garbage2garbage/shruti1/hardware/shruti/shruti1/resources.h

// Copyright 2009 Olivier Gillet.
//
// Author: Olivier Gillet (ol.gillet@gmail.com)
//
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
// -----------------------------------------------------------------------------
//
// Resources definitions.
//
// Automatically generated with:
// python arc.py resources.py


#ifndef HARDWARE_SHRUTI_SHRUTI1_RESOURCES_H_
#define HARDWARE_SHRUTI_SHRUTI1_RESOURCES_H_


#include "hardware/base/base.h"

#include <avr/pgmspace.h>


#include "hardware/resources/resources_manager.h"
namespace hardware_shruti {

typedef uint8_t ResourceId;

extern const prog_char* string_table[];

extern const prog_uint16_t* lookup_table_table[];

extern const prog_uint8_t* waveform_table[];

extern const prog_uint8_t* character_table[];

extern const prog_uint16_t lut_res_lfo_increments[] PROGMEM;
extern const prog_uint16_t lut_res_env_portamento_increments[] PROGMEM;
extern const prog_uint16_t lut_res_oscillator_increments[] PROGMEM;
extern const prog_uint16_t lut_res_fm_frequency_ratios[] PROGMEM;
extern const prog_uint16_t lut_res_scale_just[] PROGMEM;
extern const prog_uint16_t lut_res_scale_pythagorean[] PROGMEM;
extern const prog_uint16_t lut_res_scale_1_4_eb[] PROGMEM;
extern const prog_uint16_t lut_res_scale_1_4_e[] PROGMEM;
extern const prog_uint16_t lut_res_scale_1_4_ea[] PROGMEM;
extern const prog_uint16_t lut_res_scale_kanakangi[] PROGMEM;
extern const prog_uint16_t lut_res_scale_vanaspati[] PROGMEM;
extern const prog_uint16_t lut_res_scale_tanarupi[] PROGMEM;
extern const prog_uint16_t lut_res_scale_jhankaradhwani[] PROGMEM;
extern const prog_uint16_t lut_res_scale_kharaharapriya[] PROGMEM;
extern const prog_uint16_t lut_res_scale_varunapriya[] PROGMEM;
extern const prog_uint16_t lut_res_scale_yagapriya[] PROGMEM;
extern const prog_uint16_t lut_res_scale_vagadheeswari[] PROGMEM;
extern const prog_uint16_t lut_res_scale_chalanata[] PROGMEM;
extern const prog_uint16_t lut_res_arpeggiator_patterns[] PROGMEM;
extern const prog_uint8_t wav_res_formant_sine[] PROGMEM;
extern const prog_uint8_t wav_res_formant_square[] PROGMEM;
extern const prog_uint8_t wav_res_bandlimited_pulse_1[] PROGMEM;
extern const prog_uint8_t wav_res_bandlimited_pulse_2[] PROGMEM;
extern const prog_uint8_t wav_res_bandlimited_pulse_3[] PROGMEM;
extern const prog_uint8_t wav_res_bandlimited_pulse_4[] PROGMEM;
extern const prog_uint8_t wav_res_bandlimited_pulse_5[] PROGMEM;
extern const prog_uint8_t wav_res_bandlimited_pulse_6[] PROGMEM;
extern const prog_uint8_t wav_res_bandlimited_square_0[] PROGMEM;
extern const prog_uint8_t wav_res_bandlimited_square_1[] PROGMEM;
extern const prog_uint8_t wav_res_bandlimited_square_2[] PROGMEM;
extern const prog_uint8_t wav_res_bandlimited_square_3[] PROGMEM;
extern const prog_uint8_t wav_res_bandlimited_square_4[] PROGMEM;
extern const prog_uint8_t wav_res_bandlimited_square_5[] PROGMEM;
extern const prog_uint8_t wav_res_bandlimited_square_6[] PROGMEM;
extern const prog_uint8_t wav_res_bandlimited_saw_0[] PROGMEM;
extern const prog_uint8_t wav_res_bandlimited_saw_1[] PROGMEM;
extern const prog_uint8_t wav_res_bandlimited_saw_2[] PROGMEM;
extern const prog_uint8_t wav_res_bandlimited_saw_3[] PROGMEM;
extern const prog_uint8_t wav_res_bandlimited_saw_4[] PROGMEM;
extern const prog_uint8_t wav_res_bandlimited_saw_5[] PROGMEM;
extern const prog_uint8_t wav_res_bandlimited_triangle_0[] PROGMEM;
extern const prog_uint8_t wav_res_bandlimited_triangle_1[] PROGMEM;
extern const prog_uint8_t wav_res_bandlimited_triangle_2[] PROGMEM;
extern const prog_uint8_t wav_res_bandlimited_triangle_3[] PROGMEM;
extern const prog_uint8_t wav_res_bandlimited_triangle_4[] PROGMEM;
extern const prog_uint8_t wav_res_bandlimited_triangle_5[] PROGMEM;
extern const prog_uint8_t wav_res_wavetable[] PROGMEM;
extern const prog_uint8_t wav_res_vowel_data[] PROGMEM;
extern const prog_uint8_t chr_res_special_characters[] PROGMEM;
#define STR_RES_ATK 0  // atk
#define STR_RES_WV1 1  // wv1
#define STR_RES_RT1 2  // rt1
#define STR_RES_WV2 3  // wv2
#define STR_RES_RT2 4  // rt2
#define STR_RES_SRC 5  // src
#define STR_RES_DST 6  // dst
#define STR_RES_AMT 7  // amt
#define STR_RES_CHN 8  // chn
#define STR_RES_BPM 9  // bpm
#define STR_RES_SWG 10  // swg
#define STR_RES_SHAPE 11  // shape
#define STR_RES_ENV1TVCF 12  // env1~vcf
#define STR_RES_LFO2TVCF 13  // lfo2~vcf
#define STR_RES_RESONANCE 14  // resonance
#define STR_RES_ENVELOPE_1 15  // envelope 1
#define STR_RES_ENVELOPE_2 16  // envelope 2
#define STR_RES_SEQUENCER 17  // sequencer
#define STR_RES_ATTACK 18  // attack
#define STR_RES_DECAY 19  // decay
#define STR_RES_SUSTAIN 20  // sustain
#define STR_RES_RELEASE 21  // release
#define STR_RES_LFO1_WAVE 22  // lfo1 wave
#define STR_RES_LFO1_RATE 23  // lfo1 rate
#define STR_RES_LFO2_WAVE 24  // lfo2 wave
#define STR_RES_LFO2_RATE 25  // lfo2 rate
#define STR_RES_MOD_ 26  // mod.
#define STR_RES_SOURCE 27  // source
#define STR_RES_DEST_ 28  // dest.
#define STR_RES_AMOUNT 29  // amount
#define STR_RES_OCTAVE 30  // octave
#define STR_RES_RAGA 31  // raga
#define STR_RES_MIDI_CHAN 32  // midi chan
#define STR_RES_TEMPO 33  // tempo
#define STR_RES_MIXER 34  // mixer
#define STR_RES_FILTER 35  // filter
#define STR_RES_LFOS 36  // lfos
#define STR_RES_MODULATION 37  // modulation
#define STR_RES_KEYBOARD 38  // keyboard
#define STR_RES_OFF 39  // off
#define STR_RES_ON 40  // on
#define STR_RES_TRI 41  // tri
#define STR_RES_SQR 42  // sqr
#define STR_RES_S_H 43  // s&h
#define STR_RES_3 44  // 
#define STR_RES_LF1 45  // lf1
#define STR_RES_LF2 46  // lf2
#define STR_RES_SEQ 47  // seq
#define STR_RES_ARP 48  // arp
#define STR_RES_WHL 49  // whl
#define STR_RES_BND 50  // bnd
#define STR_RES_AS1 51  // as1
#define STR_RES_AS2 52  // as2
#define STR_RES_CV1 53  // cv1
#define STR_RES_CV2 54  // cv2
#define STR_RES_RND 55  // rnd
#define STR_RES_EN1 56  // en1
#define STR_RES_EN2 57  // en2
#define STR_RES_VEL 58  // vel
#define STR_RES_NOT 59  // not
#define STR_RES_GAT 60  // gat
#define STR_RES_LFO1 61  // lfo1
#define STR_RES_LFO2 62  // lfo2
#define STR_RES_STPSEQ 63  // stpseq
#define STR_RES__ARP 64  //  arp
#define STR_RES_MWHEEL 65  // mwheel
#define STR_RES_BENDER 66  // bender
#define STR_RES_ASSGN1 67  // assgn1
#define STR_RES_ASSGN2 68  // assgn2
#define STR_RES__CV1 69  //  cv1
#define STR_RES__CV2 70  //  cv2
#define STR_RES_RANDOM 71  // random
#define STR_RES_ENV1 72  // env1
#define STR_RES_ENV2 73  // env2
#define STR_RES_VELO 74  // velo
#define STR_RES_NOTE 75  // note
#define STR_RES_GATE 76  // gate
#define STR_RES_P_ORLEANS_21_MN 77  // P.ORLEANS: 21 MN
#define STR_RES_P_BERCY_____S1H 78  // P.BERCY:     +1H
#define STR_RES_LOAD_SAVE_PATCH 79  // load/save patch
#define STR_RES_STEP_SEQUENCER 80  // step sequencer
#define STR_RES_LOAD 81  // load
#define STR_RES_EXIT 82  // exit
#define STR_RES_SAVE 83  // save
#define STR_RES_EXTERN 84  // extern
#define STR_RES_EQUAL 85  // equal
#define STR_RES_JUST 86  // just
#define STR_RES_PYTHAG 87  // pythag
#define STR_RES_1_4_EB 88  // 1/4 eb
#define STR_RES_1_4_E 89  // 1/4 e
#define STR_RES_1_4_EA 90  // 1/4 ea
#define STR_RES_KANAKA 91  // kanaka
#define STR_RES_RATNAN 92  // ratnan
#define STR_RES_GANAMU 93  // ganamu
#define STR_RES_VANASP 94  // vanasp
#define STR_RES_MANAVA 95  // manava
#define STR_RES_TANARU 96  // tanaru
#define STR_RES_SENAVA 97  // senava
#define STR_RES_HANUMA 98  // hanuma
#define STR_RES_DHENUK 99  // dhenuk
#define STR_RES_NATAKA 100  // nataka
#define STR_RES_KOKILA 101  // kokila
#define STR_RES_RUPAVA 102  // rupava
#define STR_RES_GAYAKA 103  // gayaka
#define STR_RES_VAKULA 104  // vakula
#define STR_RES_MAYAMA 105  // mayama
#define STR_RES_CHAKRA 106  // chakra
#define STR_RES_SURYAK 107  // suryak
#define STR_RES_HATAKA 108  // hataka
#define STR_RES_JHANKA 109  // jhanka
#define STR_RES_NATABH 110  // natabh
#define STR_RES_KEERAV 111  // keerav
#define STR_RES_KHARAH 112  // kharah
#define STR_RES_GOURIM 113  // gourim
#define STR_RES_VARUNA 114  // varuna
#define STR_RES_MARARA 115  // marara
#define STR_RES_CHARUK 116  // charuk
#define STR_RES_SARASA 117  // sarasa
#define STR_RES_HARIKA 118  // harika
#define STR_RES_DHEERA 119  // dheera
#define STR_RES_NAGANA 120  // nagana
#define STR_RES_YAGAPR 121  // yagapr
#define STR_RES_RAGAVA 122  // ragava
#define STR_RES_GANGEY 123  // gangey
#define STR_RES_VAGADH 124  // vagadh
#define STR_RES_SHULIN 125  // shulin
#define STR_RES_CHALAN 126  // chalan
#define STR_RES_SALAGA 127  // salaga
#define STR_RES_JALARN 128  // jalarn
#define STR_RES_JHALAV 129  // jhalav
#define STR_RES_NAVANE 130  // navane
#define STR_RES_PAVANI 131  // pavani
#define STR_RES_RAGHUP 132  // raghup
#define STR_RES_GAVAMB 133  // gavamb
#define STR_RES_BHAVAP 134  // bhavap
#define STR_RES_SHUBHA 135  // shubha
#define STR_RES_SHADVI 136  // shadvi
#define STR_RES_SUVARN 137  // suvarn
#define STR_RES_DIVYAM 138  // divyam
#define STR_RES_DHAVAL 139  // dhaval
#define STR_RES_NAMANA 140  // namana
#define STR_RES_KAMAVA 141  // kamava
#define STR_RES_RAMAPR 142  // ramapr
#define STR_RES_GAMANA 143  // gamana
#define STR_RES_VISHWA 144  // vishwa
#define STR_RES_SHAMAL 145  // shamal
#define STR_RES_SHANMU 146  // shanmu
#define STR_RES_SIMHEN 147  // simhen
#define STR_RES_HEMAVA 148  // hemava
#define STR_RES_DHARMA 149  // dharma
#define STR_RES_NEETIM 150  // neetim
#define STR_RES_KANTAM 151  // kantam
#define STR_RES_RISHAB 152  // rishab
#define STR_RES_LATANG 153  // latang
#define STR_RES_VACHAS 154  // vachas
#define STR_RES_MECHAK 155  // mechak
#define STR_RES_CHITRA 156  // chitra
#define STR_RES_SUCHAR 157  // suchar
#define STR_RES_JYOTIS 158  // jyotis
#define STR_RES_DHATUV 159  // dhatuv
#define STR_RES_NASIKA 160  // nasika
#define STR_RES_KOSALA 161  // kosala
#define STR_RES_RASIKA 162  // rasika
#define STR_RES_PRM 163  // prm
#define STR_RES_RNG 164  // rng
#define STR_RES_OP 165  // op
#define STR_RES_TUN 166  // tun
#define STR_RES_PRT 167  // prt
#define STR_RES_PORTA 168  // porta
#define STR_RES_PARAMETER 169  // parameter
#define STR_RES_RANGE 170  // range
#define STR_RES_OPERATOR 171  // operator
#define STR_RES_DETUNE 172  // detune
#define STR_RES_OSC_BAL 173  // osc bal
#define STR_RES_SUB_OSC_ 174  // sub osc.
#define STR_RES_PATTERN 175  // pattern
#define STR_RES_SWING 176  // swing
#define STR_RES_OSCILLATOR_1 177  // oscillator 1
#define STR_RES_OSCILLATOR_2 178  // oscillator 2
#define STR_RES_ARPEGGIO 179  // arpeggio
#define STR_RES_NONE 180  // none
#define STR_RES_BLIT 181  // blit
#define STR_RES_SAW 182  // saw
#define STR_RES_SQUARE 183  // square
#define STR_RES_TRIANG 184  // triang
#define STR_RES_CZ 185  // cz
#define STR_RES_FM 186  // fm
#define STR_RES_8BITS 187  // 8bits
#define STR_RES_PWM 188  // pwm
#define STR_RES_NOISE 189  // noise
#define STR_RES_VOWEL 190  // vowel
#define STR_RES_TABLE 191  // table
#define STR_RES_SWEEP 192  // sweep
#define STR_RES_1S2 193  // 1+2
#define STR_RES_1_2 194  // 1>2
#define STR_RES_1P2 195  // 1*2
#define STR_RES_1X2 196  // 1^2
#define STR_RES_CUT 197  // cut
#define STR_RES_VCA 198  // vca
#define STR_RES_PW1 199  // pw1
#define STR_RES_PW2 200  // pw2
#define STR_RES_51 201  // 1
#define STR_RES_52 202  // 2
#define STR_RES_5 203  // 
#define STR_RES_MIX 204  // mix
#define STR_RES_NOI 205  // noi
#define STR_RES_SUB 206  // sub
#define STR_RES_RES 207  // res
#define STR_RES_CUTOFF 208  // cutoff
#define STR_RES__VCA 209  //  vca
#define STR_RES_PWM1 210  // pwm1
#define STR_RES_PWM2 211  // pwm2
#define STR_RES_OSC1 212  // osc1
#define STR_RES_OSC2 213  // osc2
#define STR_RES_OSC1S2 214  // osc1+2
#define STR_RES__MIX 215  //  mix
#define STR_RES__NOISE 216  //  noise
#define STR_RES_SUBOSC 217  // subosc
#define STR_RES_RESO 218  // reso
#define STR_RES_MUTABLE 219  // mutable
#define STR_RES_INSTRUMENTS_671 220  // instruments -1
#define LUT_RES_LFO_INCREMENTS 0
#define LUT_RES_LFO_INCREMENTS_SIZE 128
#define LUT_RES_ENV_PORTAMENTO_INCREMENTS 1
#define LUT_RES_ENV_PORTAMENTO_INCREMENTS_SIZE 128
#define LUT_RES_OSCILLATOR_INCREMENTS 2
#define LUT_RES_OSCILLATOR_INCREMENTS_SIZE 768
#define LUT_RES_FM_FREQUENCY_RATIOS 3
#define LUT_RES_FM_FREQUENCY_RATIOS_SIZE 25
#define LUT_RES_SCALE_JUST 4
#define LUT_RES_SCALE_JUST_SIZE 12
#define LUT_RES_SCALE_PYTHAGOREAN 5
#define LUT_RES_SCALE_PYTHAGOREAN_SIZE 12
#define LUT_RES_SCALE_1_4_EB 6
#define LUT_RES_SCALE_1_4_EB_SIZE 12
#define LUT_RES_SCALE_1_4_E 7
#define LUT_RES_SCALE_1_4_E_SIZE 12
#define LUT_RES_SCALE_1_4_EA 8
#define LUT_RES_SCALE_1_4_EA_SIZE 12
#define LUT_RES_SCALE_KANAKANGI 9
#define LUT_RES_SCALE_KANAKANGI_SIZE 12
#define LUT_RES_SCALE_RATNANGI 10
#define LUT_RES_SCALE_RATNANGI_SIZE 12
#define LUT_RES_SCALE_GANAMURTI 11
#define LUT_RES_SCALE_GANAMURTI_SIZE 12
#define LUT_RES_SCALE_VANASPATI 12
#define LUT_RES_SCALE_VANASPATI_SIZE 12
#define LUT_RES_SCALE_MANAVATI 13
#define LUT_RES_SCALE_MANAVATI_SIZE 12
#define LUT_RES_SCALE_TANARUPI 14
#define LUT_RES_SCALE_TANARUPI_SIZE 12
#define LUT_RES_SCALE_SENAVATI 15
#define LUT_RES_SCALE_SENAVATI_SIZE 12
#define LUT_RES_SCALE_HANUMATODI 16
#define LUT_RES_SCALE_HANUMATODI_SIZE 12
#define LUT_RES_SCALE_DHENUKA 17
#define LUT_RES_SCALE_DHENUKA_SIZE 12
#define LUT_RES_SCALE_NATAKAPRIYA 18
#define LUT_RES_SCALE_NATAKAPRIYA_SIZE 12
#define LUT_RES_SCALE_KOKILAPRIYA 19
#define LUT_RES_SCALE_KOKILAPRIYA_SIZE 12
#define LUT_RES_SCALE_RUPAVATI 20
#define LUT_RES_SCALE_RUPAVATI_SIZE 12
#define LUT_RES_SCALE_GAYAKAPRIYA 21
#define LUT_RES_SCALE_GAYAKAPRIYA_SIZE 12
#define LUT_RES_SCALE_VAKULABHARANAM 22
#define LUT_RES_SCALE_VAKULABHARANAM_SIZE 12
#define LUT_RES_SCALE_MAYAMALAVAGOWLA 23
#define LUT_RES_SCALE_MAYAMALAVAGOWLA_SIZE 12
#define LUT_RES_SCALE_CHAKRAVAKAM 24
#define LUT_RES_SCALE_CHAKRAVAKAM_SIZE 12
#define LUT_RES_SCALE_SURYAKANTAM 25
#define LUT_RES_SCALE_SURYAKANTAM_SIZE 12
#define LUT_RES_SCALE_HATAKAMBARI 26
#define LUT_RES_SCALE_HATAKAMBARI_SIZE 12
#define LUT_RES_SCALE_JHANKARADHWANI 27
#define LUT_RES_SCALE_JHANKARADHWANI_SIZE 12
#define LUT_RES_SCALE_NATABHAIRAVI 28
#define LUT_RES_SCALE_NATABHAIRAVI_SIZE 12
#define LUT_RES_SCALE_KEERAVANI 29
#define LUT_RES_SCALE_KEERAVANI_SIZE 12
#define LUT_RES_SCALE_KHARAHARAPRIYA 30
#define LUT_RES_SCALE_KHARAHARAPRIYA_SIZE 12
#define LUT_RES_SCALE_GOURIMANOHARI 31
#define LUT_RES_SCALE_GOURIMANOHARI_SIZE 12
#define LUT_RES_SCALE_VARUNAPRIYA 32
#define LUT_RES_SCALE_VARUNAPRIYA_SIZE 12
#define LUT_RES_SCALE_MARARANJANI 33
#define LUT_RES_SCALE_MARARANJANI_SIZE 12
#define LUT_RES_SCALE_CHARUKESI 34
#define LUT_RES_SCALE_CHARUKESI_SIZE 12
#define LUT_RES_SCALE_SARASANGI 35
#define LUT_RES_SCALE_SARASANGI_SIZE 12
#define LUT_RES_SCALE_HARIKAMBHOJI 36
#define LUT_RES_SCALE_HARIKAMBHOJI_SIZE 12
#define LUT_RES_SCALE_DHEERASANKARABHARANAM 37
#define LUT_RES_SCALE_DHEERASANKARABHARANAM_SIZE 12
#define LUT_RES_SCALE_NAGANANDINI 38
#define LUT_RES_SCALE_NAGANANDINI_SIZE 12
#define LUT_RES_SCALE_YAGAPRIYA 39
#define LUT_RES_SCALE_YAGAPRIYA_SIZE 12
#define LUT_RES_SCALE_RAGAVARDHINI 40
#define LUT_RES_SCALE_RAGAVARDHINI_SIZE 12
#define LUT_RES_SCALE_GANGEYABHUSHANI 41
#define LUT_RES_SCALE_GANGEYABHUSHANI_SIZE 12
#define LUT_RES_SCALE_VAGADHEESWARI 42
#define LUT_RES_SCALE_VAGADHEESWARI_SIZE 12
#define LUT_RES_SCALE_SHULINI 43
#define LUT_RES_SCALE_SHULINI_SIZE 12
#define LUT_RES_SCALE_CHALANATA 44
#define LUT_RES_SCALE_CHALANATA_SIZE 12
#define LUT_RES_SCALE_SALAGAM 45
#define LUT_RES_SCALE_SALAGAM_SIZE 12
#define LUT_RES_SCALE_JALARNAVAM 46
#define LUT_RES_SCALE_JALARNAVAM_SIZE 12
#define LUT_RES_SCALE_JHALAVARALI 47
#define LUT_RES_SCALE_JHALAVARALI_SIZE 12
#define LUT_RES_SCALE_NAVANEETAM 48
#define LUT_RES_SCALE_NAVANEETAM_SIZE 12
#define LUT_RES_SCALE_PAVANI 49
#define LUT_RES_SCALE_PAVANI_SIZE 12
#define LUT_RES_SCALE_RAGHUPRIYA 50
#define LUT_RES_SCALE_RAGHUPRIYA_SIZE 12
#define LUT_RES_SCALE_GAVAMBHODI 51
#define LUT_RES_SCALE_GAVAMBHODI_SIZE 12
#define LUT_RES_SCALE_BHAVAPRIYA 52
#define LUT_RES_SCALE_BHAVAPRIYA_SIZE 12
#define LUT_RES_SCALE_SHUBHAPANTUVARALI 53
#define LUT_RES_SCALE_SHUBHAPANTUVARALI_SIZE 12
#define LUT_RES_SCALE_SHADVIDAMARGINI 54
#define LUT_RES_SCALE_SHADVIDAMARGINI_SIZE 12
#define LUT_RES_SCALE_SUVARNANGI 55
#define LUT_RES_SCALE_SUVARNANGI_SIZE 12
#define LUT_RES_SCALE_DIVYAMANI 56
#define LUT_RES_SCALE_DIVYAMANI_SIZE 12
#define LUT_RES_SCALE_DHAVALAMBARI 57
#define LUT_RES_SCALE_DHAVALAMBARI_SIZE 12
#define LUT_RES_SCALE_NAMANARAYANI 58
#define LUT_RES_SCALE_NAMANARAYANI_SIZE 12
#define LUT_RES_SCALE_KAMAVARDANI 59
#define LUT_RES_SCALE_KAMAVARDANI_SIZE 12
#define LUT_RES_SCALE_RAMAPRIYA 60
#define LUT_RES_SCALE_RAMAPRIYA_SIZE 12
#define LUT_RES_SCALE_GAMANASHRAMA 61
#define LUT_RES_SCALE_GAMANASHRAMA_SIZE 12
#define LUT_RES_SCALE_VISHWAMBARI 62
#define LUT_RES_SCALE_VISHWAMBARI_SIZE 12
#define LUT_RES_SCALE_SHAMALANGI 63
#define LUT_RES_SCALE_SHAMALANGI_SIZE 12
#define LUT_RES_SCALE_SHANMUKHAPRIYA 64
#define LUT_RES_SCALE_SHANMUKHAPRIYA_SIZE 12
#define LUT_RES_SCALE_SIMHENDRAMADHYAMAM 65
#define LUT_RES_SCALE_SIMHENDRAMADHYAMAM_SIZE 12
#define LUT_RES_SCALE_HEMAVATI 66
#define LUT_RES_SCALE_HEMAVATI_SIZE 12
#define LUT_RES_SCALE_DHARMAVATI 67
#define LUT_RES_SCALE_DHARMAVATI_SIZE 12
#define LUT_RES_SCALE_NEETIMATI 68
#define LUT_RES_SCALE_NEETIMATI_SIZE 12
#define LUT_RES_SCALE_KANTAMANI 69
#define LUT_RES_SCALE_KANTAMANI_SIZE 12
#define LUT_RES_SCALE_RISHABHAPRIYA 70
#define LUT_RES_SCALE_RISHABHAPRIYA_SIZE 12
#define LUT_RES_SCALE_LATANGI 71
#define LUT_RES_SCALE_LATANGI_SIZE 12
#define LUT_RES_SCALE_VACHASPATI 72
#define LUT_RES_SCALE_VACHASPATI_SIZE 12
#define LUT_RES_SCALE_MECHAKALYANI 73
#define LUT_RES_SCALE_MECHAKALYANI_SIZE 12
#define LUT_RES_SCALE_CHITRAMBARI 74
#define LUT_RES_SCALE_CHITRAMBARI_SIZE 12
#define LUT_RES_SCALE_SUCHARITRA 75
#define LUT_RES_SCALE_SUCHARITRA_SIZE 12
#define LUT_RES_SCALE_JYOTISWARUPINI 76
#define LUT_RES_SCALE_JYOTISWARUPINI_SIZE 12
#define LUT_RES_SCALE_DHATUVARDANI 77
#define LUT_RES_SCALE_DHATUVARDANI_SIZE 12
#define LUT_RES_SCALE_NASIKABHUSHANI 78
#define LUT_RES_SCALE_NASIKABHUSHANI_SIZE 12
#define LUT_RES_SCALE_KOSALAM 79
#define LUT_RES_SCALE_KOSALAM_SIZE 12
#define LUT_RES_SCALE_RASIKAPRIYA 80
#define LUT_RES_SCALE_RASIKAPRIYA_SIZE 12
#define LUT_RES_ARPEGGIATOR_PATTERNS 81
#define LUT_RES_ARPEGGIATOR_PATTERNS_SIZE 15
#define WAV_RES_FORMANT_SINE 0
#define WAV_RES_FORMANT_SINE_SIZE 256
#define WAV_RES_FORMANT_SQUARE 1
#define WAV_RES_FORMANT_SQUARE_SIZE 256
#define WAV_RES_BANDLIMITED_PULSE_1 2
#define WAV_RES_BANDLIMITED_PULSE_1_SIZE 257
#define WAV_RES_BANDLIMITED_PULSE_2 3
#define WAV_RES_BANDLIMITED_PULSE_2_SIZE 257
#define WAV_RES_BANDLIMITED_PULSE_3 4
#define WAV_RES_BANDLIMITED_PULSE_3_SIZE 257
#define WAV_RES_BANDLIMITED_PULSE_4 5
#define WAV_RES_BANDLIMITED_PULSE_4_SIZE 257
#define WAV_RES_BANDLIMITED_PULSE_5 6
#define WAV_RES_BANDLIMITED_PULSE_5_SIZE 257
#define WAV_RES_BANDLIMITED_PULSE_6 7
#define WAV_RES_BANDLIMITED_PULSE_6_SIZE 257
#define WAV_RES_BANDLIMITED_SQUARE_0 8
#define WAV_RES_BANDLIMITED_SQUARE_0_SIZE 257
#define WAV_RES_BANDLIMITED_SQUARE_1 9
#define WAV_RES_BANDLIMITED_SQUARE_1_SIZE 257
#define WAV_RES_BANDLIMITED_SQUARE_2 10
#define WAV_RES_BANDLIMITED_SQUARE_2_SIZE 257
#define WAV_RES_BANDLIMITED_SQUARE_3 11
#define WAV_RES_BANDLIMITED_SQUARE_3_SIZE 257
#define WAV_RES_BANDLIMITED_SQUARE_4 12
#define WAV_RES_BANDLIMITED_SQUARE_4_SIZE 257
#define WAV_RES_BANDLIMITED_SQUARE_5 13
#define WAV_RES_BANDLIMITED_SQUARE_5_SIZE 257
#define WAV_RES_BANDLIMITED_SQUARE_6 14
#define WAV_RES_BANDLIMITED_SQUARE_6_SIZE 257
#define WAV_RES_BANDLIMITED_SAW_0 15
#define WAV_RES_BANDLIMITED_SAW_0_SIZE 257
#define WAV_RES_BANDLIMITED_SAW_1 16
#define WAV_RES_BANDLIMITED_SAW_1_SIZE 257
#define WAV_RES_BANDLIMITED_SAW_2 17
#define WAV_RES_BANDLIMITED_SAW_2_SIZE 257
#define WAV_RES_BANDLIMITED_SAW_3 18
#define WAV_RES_BANDLIMITED_SAW_3_SIZE 257
#define WAV_RES_BANDLIMITED_SAW_4 19
#define WAV_RES_BANDLIMITED_SAW_4_SIZE 257
#define WAV_RES_BANDLIMITED_SAW_5 20
#define WAV_RES_BANDLIMITED_SAW_5_SIZE 257
#define WAV_RES_BANDLIMITED_SAW_6 21
#define WAV_RES_BANDLIMITED_SAW_6_SIZE 257
#define WAV_RES_BANDLIMITED_TRIANGLE_0 22
#define WAV_RES_BANDLIMITED_TRIANGLE_0_SIZE 257
#define WAV_RES_BANDLIMITED_TRIANGLE_1 23
#define WAV_RES_BANDLIMITED_TRIANGLE_1_SIZE 257
#define WAV_RES_BANDLIMITED_TRIANGLE_2 24
#define WAV_RES_BANDLIMITED_TRIANGLE_2_SIZE 257
#define WAV_RES_BANDLIMITED_TRIANGLE_3 25
#define WAV_RES_BANDLIMITED_TRIANGLE_3_SIZE 257
#define WAV_RES_BANDLIMITED_TRIANGLE_4 26
#define WAV_RES_BANDLIMITED_TRIANGLE_4_SIZE 257
#define WAV_RES_BANDLIMITED_TRIANGLE_5 27
#define WAV_RES_BANDLIMITED_TRIANGLE_5_SIZE 257
#define WAV_RES_BANDLIMITED_TRIANGLE_6 28
#define WAV_RES_BANDLIMITED_TRIANGLE_6_SIZE 257
#define WAV_RES_WAVETABLE 29
#define WAV_RES_WAVETABLE_SIZE 2145
#define WAV_RES_VOWEL_DATA 30
#define WAV_RES_VOWEL_DATA_SIZE 45
#define CHR_RES_SPECIAL_CHARACTERS 0
#define CHR_RES_SPECIAL_CHARACTERS_SIZE 64
typedef hardware_resources::ResourcesManager<
    ResourceId,
    hardware_resources::ResourcesTables<
        string_table,
        lookup_table_table> > ResourcesManager; 

}  // namespace hardware_shruti

#endif  // HARDWARE_SHRUTI_SHRUTI1_RESOURCES_H_
