garbage2garbage/shruti1/hardware/shruti/resources.cc

// Copyright 2009 Emilie Gillet.
//
// Author: Emilie Gillet (emilie.o.gillet@gmail.com)
//
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
// -----------------------------------------------------------------------------
//
// Resources definitions.
//
// Automatically generated with:
// make resources


#include "resources.h"

namespace hardware_shruti {

static const prog_char str_res_prm[] PROGMEM = "prm";
static const prog_char str_res_rng[] PROGMEM = "rng";
static const prog_char str_res_op[] PROGMEM = "op";
static const prog_char str_res_tun[] PROGMEM = "tun";
static const prog_char str_res_prt[] PROGMEM = "prt";
static const prog_char str_res_porta[] PROGMEM = "porta";
static const prog_char str_res_parameter[] PROGMEM = "parameter";
static const prog_char str_res_range[] PROGMEM = "range";
static const prog_char str_res_operator[] PROGMEM = "operator";
static const prog_char str_res_detune[] PROGMEM = "detune";
static const prog_char str_res_osc_bal[] PROGMEM = "osc bal";
static const prog_char str_res_sub_osc_[] PROGMEM = "sub osc.";
static const prog_char str_res_pattern[] PROGMEM = "pattern";
static const prog_char str_res_groove[] PROGMEM = "groove";
static const prog_char str_res_oscillator_1[] PROGMEM = "oscillator 1";
static const prog_char str_res_oscillator_2[] PROGMEM = "oscillator 2";
static const prog_char str_res_arpeggio[] PROGMEM = "arpeggio";
static const prog_char str_res_performance[] PROGMEM = "performance";
static const prog_char str_res_none[] PROGMEM = "none";
static const prog_char str_res_blit[] PROGMEM = "blit";
static const prog_char str_res_saw[] PROGMEM = "saw";
static const prog_char str_res_square[] PROGMEM = "square";
static const prog_char str_res_triang[] PROGMEM = "triang";
static const prog_char str_res_cz[] PROGMEM = "cz";
static const prog_char str_res_fm[] PROGMEM = "fm";
static const prog_char str_res_8bits[] PROGMEM = "8bits";
static const prog_char str_res_pwm[] PROGMEM = "pwm";
static const prog_char str_res_noise[] PROGMEM = "noise";
static const prog_char str_res_vowel[] PROGMEM = "vowel";
static const prog_char str_res_wavtbl[] PROGMEM = "wavtbl";
static const prog_char str_res_sweep[] PROGMEM = "sweep";
static const prog_char str_res_zsync[] PROGMEM = "zsync";
static const prog_char str_res_pad[] PROGMEM = "pad";
static const prog_char str_res_1S2[] PROGMEM = "1+2";
static const prog_char str_res_1_2[] PROGMEM = "1>2";
static const prog_char str_res_1P2[] PROGMEM = "1*2";
static const prog_char str_res_1x2[] PROGMEM = "1^2";
static const prog_char str_res_cut[] PROGMEM = "cut";
static const prog_char str_res_vca[] PROGMEM = "vca";
static const prog_char str_res_pw1[] PROGMEM = "pw1";
static const prog_char str_res_pw2[] PROGMEM = "pw2";
static const prog_char str_res_51[] PROGMEM = "1";
static const prog_char str_res_52[] PROGMEM = "2";
static const prog_char str_res_5[] PROGMEM = "";
static const prog_char str_res_mix[] PROGMEM = "mix";
static const prog_char str_res_noi[] PROGMEM = "noi";
static const prog_char str_res_sub[] PROGMEM = "sub";
static const prog_char str_res_res[] PROGMEM = "res";
static const prog_char str_res_cutoff[] PROGMEM = "cutoff";
static const prog_char str_res__vca[] PROGMEM = "vca";
static const prog_char str_res_pwm1[] PROGMEM = "pwm1";
static const prog_char str_res_pwm2[] PROGMEM = "pwm2";
static const prog_char str_res_osc1[] PROGMEM = "osc1";
static const prog_char str_res_osc2[] PROGMEM = "osc2";
static const prog_char str_res_osc1S2[] PROGMEM = "osc1+2";
static const prog_char str_res__mix[] PROGMEM = "mix";
static const prog_char str_res__noise[] PROGMEM = "noise";
static const prog_char str_res_subosc[] PROGMEM = "subosc";
static const prog_char str_res_reso[] PROGMEM = "reso";
static const prog_char str_res_atk[] PROGMEM = "atk";
static const prog_char str_res_wv1[] PROGMEM = "wv1";
static const prog_char str_res_rt1[] PROGMEM = "rt1";
static const prog_char str_res_wv2[] PROGMEM = "wv2";
static const prog_char str_res_rt2[] PROGMEM = "rt2";
static const prog_char str_res_src[] PROGMEM = "src";
static const prog_char str_res_dst[] PROGMEM = "dst";
static const prog_char str_res_amt[] PROGMEM = "amt";
static const prog_char str_res_chn[] PROGMEM = "chn";
static const prog_char str_res_bpm[] PROGMEM = "bpm";
static const prog_char str_res_swg[] PROGMEM = "swg";
static const prog_char str_res_shape[] PROGMEM = "shape";
static const prog_char str_res_env1Tvcf[] PROGMEM = "env1~vcf";
static const prog_char str_res_lfo2Tvcf[] PROGMEM = "lfo2~vcf";
static const prog_char str_res_resonance[] PROGMEM = "resonance";
static const prog_char str_res_envelope_1[] PROGMEM = "envelope 1";
static const prog_char str_res_envelope_2[] PROGMEM = "envelope 2";
static const prog_char str_res_sequencer[] PROGMEM = "sequencer";
static const prog_char str_res_attack[] PROGMEM = "attack";
static const prog_char str_res_decay[] PROGMEM = "decay";
static const prog_char str_res_sustain[] PROGMEM = "sustain";
static const prog_char str_res_release[] PROGMEM = "release";
static const prog_char str_res_lfo1_wave[] PROGMEM = "lfo1 wave";
static const prog_char str_res_lfo1_rate[] PROGMEM = "lfo1 rate";
static const prog_char str_res_lfo2_wave[] PROGMEM = "lfo2 wave";
static const prog_char str_res_lfo2_rate[] PROGMEM = "lfo2 rate";
static const prog_char str_res_mod_[] PROGMEM = "mod.";
static const prog_char str_res_source[] PROGMEM = "source";
static const prog_char str_res_dest_[] PROGMEM = "dest.";
static const prog_char str_res_amount[] PROGMEM = "amount";
static const prog_char str_res_octave[] PROGMEM = "octave";
static const prog_char str_res_raga[] PROGMEM = "raga";
static const prog_char str_res_midi_chan[] PROGMEM = "midi chan";
static const prog_char str_res_tempo[] PROGMEM = "tempo";
static const prog_char str_res_mixer[] PROGMEM = "mixer";
static const prog_char str_res_filter[] PROGMEM = "filter";
static const prog_char str_res_lfos[] PROGMEM = "lfos";
static const prog_char str_res_modulation[] PROGMEM = "modulation";
static const prog_char str_res_keyboard[] PROGMEM = "keyboard";
static const prog_char str_res_off[] PROGMEM = "off";
static const prog_char str_res_on[] PROGMEM = "on";
static const prog_char str_res_tri[] PROGMEM = "tri";
static const prog_char str_res_sqr[] PROGMEM = "sqr";
static const prog_char str_res_s_h[] PROGMEM = "s&h";
static const prog_char str_res_3[] PROGMEM = "";
static const prog_char str_res__seq[] PROGMEM = "seq";
static const prog_char str_res_lf1[] PROGMEM = "lf1";
static const prog_char str_res_lf2[] PROGMEM = "lf2";
static const prog_char str_res_seq[] PROGMEM = "seq";
static const prog_char str_res_arp[] PROGMEM = "arp";
static const prog_char str_res_whl[] PROGMEM = "whl";
static const prog_char str_res_bnd[] PROGMEM = "bnd";
static const prog_char str_res_ofs[] PROGMEM = "ofs";
static const prog_char str_res_cv1[] PROGMEM = "cv1";
static const prog_char str_res_cv2[] PROGMEM = "cv2";
static const prog_char str_res_cv3[] PROGMEM = "cv3";
static const prog_char str_res_rnd[] PROGMEM = "rnd";
static const prog_char str_res_en1[] PROGMEM = "en1";
static const prog_char str_res_en2[] PROGMEM = "en2";
static const prog_char str_res_vel[] PROGMEM = "vel";
static const prog_char str_res_not[] PROGMEM = "not";
static const prog_char str_res_gat[] PROGMEM = "gat";
static const prog_char str_res_lfo1[] PROGMEM = "lfo1";
static const prog_char str_res_lfo2[] PROGMEM = "lfo2";
static const prog_char str_res_stpseq[] PROGMEM = "stpseq";
static const prog_char str_res__arp[] PROGMEM = "arp";
static const prog_char str_res_mwheel[] PROGMEM = "mwheel";
static const prog_char str_res_bender[] PROGMEM = "bender";
static const prog_char str_res_offset[] PROGMEM = "offset";
static const prog_char str_res__cv1[] PROGMEM = "cv1";
static const prog_char str_res__cv2[] PROGMEM = "cv2";
static const prog_char str_res__cv3[] PROGMEM = "cv3";
static const prog_char str_res_random[] PROGMEM = "random";
static const prog_char str_res_env1[] PROGMEM = "env1";
static const prog_char str_res_env2[] PROGMEM = "env2";
static const prog_char str_res_velo[] PROGMEM = "velo";
static const prog_char str_res_note[] PROGMEM = "note";
static const prog_char str_res_gate[] PROGMEM = "gate";
static const prog_char str_res_270[] PROGMEM = "270";
static const prog_char str_res_300[] PROGMEM = "300";
static const prog_char str_res_360[] PROGMEM = "360";
static const prog_char str_res_480[] PROGMEM = "480";
static const prog_char str_res_720[] PROGMEM = "720";
static const prog_char str_res_960[] PROGMEM = "960";
static const prog_char str_res_start[] PROGMEM = "start";
static const prog_char str_res_length[] PROGMEM = "length";
static const prog_char str_res_touch_a_knob_to[] PROGMEM = "touch a knob to";
static const prog_char str_res_assign_parameter[] PROGMEM = "assign parameter";
static const prog_char str_res_ready[] PROGMEM = "ready";
static const prog_char str_res_for_os_update[] PROGMEM = "for os update";
static const prog_char str_res_patch_bank[] PROGMEM = "patch bank";
static const prog_char str_res_step_sequencer[] PROGMEM = "step sequencer";
static const prog_char str_res_load[] PROGMEM = "load";
static const prog_char str_res_[] PROGMEM = "----";
static const prog_char str_res_save[] PROGMEM = "save";
static const prog_char str_res_extern[] PROGMEM = "extern";
static const prog_char str_res_x2_ext[] PROGMEM = "x2 ext";
static const prog_char str_res__2_ext[] PROGMEM = "/2 ext";
static const prog_char str_res__4_ext[] PROGMEM = "/4 ext";
static const prog_char str_res__8_ext[] PROGMEM = "/8 ext";
static const prog_char str_res_mutable____v0_59[] PROGMEM = "mutable    v0.59";
static const prog_char str_res_instruments_671[] PROGMEM = "instruments -1";
static const prog_char str_res_equal[] PROGMEM = "equal";
static const prog_char str_res_just[] PROGMEM = "just";
static const prog_char str_res_pythag[] PROGMEM = "pythag";
static const prog_char str_res_1_4_eb[] PROGMEM = "1/4 eb";
static const prog_char str_res_1_4_e[] PROGMEM = "1/4 e";
static const prog_char str_res_1_4_ea[] PROGMEM = "1/4 ea";
static const prog_char str_res_bhaira[] PROGMEM = "bhaira";
static const prog_char str_res_gunakr[] PROGMEM = "gunakr";
static const prog_char str_res_marwa[] PROGMEM = "marwa";
static const prog_char str_res_shree[] PROGMEM = "shree";
static const prog_char str_res_purvi[] PROGMEM = "purvi";
static const prog_char str_res_bilawa[] PROGMEM = "bilawa";
static const prog_char str_res_yaman[] PROGMEM = "yaman";
static const prog_char str_res_kafi[] PROGMEM = "kafi";
static const prog_char str_res_bhimpa[] PROGMEM = "bhimpa";
static const prog_char str_res_darbar[] PROGMEM = "darbar";
static const prog_char str_res_bagesh[] PROGMEM = "bagesh";
static const prog_char str_res_ragesh[] PROGMEM = "ragesh";
static const prog_char str_res_khamaj[] PROGMEM = "khamaj";
static const prog_char str_res_mimal[] PROGMEM = "mi'mal";
static const prog_char str_res_parame[] PROGMEM = "parame";
static const prog_char str_res_ranges[] PROGMEM = "ranges";
static const prog_char str_res_ganges[] PROGMEM = "ganges";
static const prog_char str_res_kamesh[] PROGMEM = "kamesh";
static const prog_char str_res_palas_[] PROGMEM = "palas";
static const prog_char str_res_natbha[] PROGMEM = "natbha";
static const prog_char str_res_m_kaun[] PROGMEM = "m.kaun";
static const prog_char str_res_bairag[] PROGMEM = "bairag";
static const prog_char str_res_b_todi[] PROGMEM = "b.todi";
static const prog_char str_res_chandr[] PROGMEM = "chandr";
static const prog_char str_res_kaushi[] PROGMEM = "kaushi";
static const prog_char str_res_jogesh[] PROGMEM = "jogesh";
static const prog_char str_res_rasia[] PROGMEM = "rasia";


PROGMEM const prog_char* string_table[] = {
  str_res_prm,
  str_res_rng,
  str_res_op,
  str_res_tun,
  str_res_prt,
  str_res_porta,
  str_res_parameter,
  str_res_range,
  str_res_operator,
  str_res_detune,
  str_res_osc_bal,
  str_res_sub_osc_,
  str_res_pattern,
  str_res_groove,
  str_res_oscillator_1,
  str_res_oscillator_2,
  str_res_arpeggio,
  str_res_performance,
  str_res_none,
  str_res_blit,
  str_res_saw,
  str_res_square,
  str_res_triang,
  str_res_cz,
  str_res_fm,
  str_res_8bits,
  str_res_pwm,
  str_res_noise,
  str_res_vowel,
  str_res_wavtbl,
  str_res_sweep,
  str_res_zsync,
  str_res_pad,
  str_res_1S2,
  str_res_1_2,
  str_res_1P2,
  str_res_1x2,
  str_res_cut,
  str_res_vca,
  str_res_pw1,
  str_res_pw2,
  str_res_51,
  str_res_52,
  str_res_5,
  str_res_mix,
  str_res_noi,
  str_res_sub,
  str_res_res,
  str_res_cutoff,
  str_res__vca,
  str_res_pwm1,
  str_res_pwm2,
  str_res_osc1,
  str_res_osc2,
  str_res_osc1S2,
  str_res__mix,
  str_res__noise,
  str_res_subosc,
  str_res_reso,
  str_res_atk,
  str_res_wv1,
  str_res_rt1,
  str_res_wv2,
  str_res_rt2,
  str_res_src,
  str_res_dst,
  str_res_amt,
  str_res_chn,
  str_res_bpm,
  str_res_swg,
  str_res_shape,
  str_res_env1Tvcf,
  str_res_lfo2Tvcf,
  str_res_resonance,
  str_res_envelope_1,
  str_res_envelope_2,
  str_res_sequencer,
  str_res_attack,
  str_res_decay,
  str_res_sustain,
  str_res_release,
  str_res_lfo1_wave,
  str_res_lfo1_rate,
  str_res_lfo2_wave,
  str_res_lfo2_rate,
  str_res_mod_,
  str_res_source,
  str_res_dest_,
  str_res_amount,
  str_res_octave,
  str_res_raga,
  str_res_midi_chan,
  str_res_tempo,
  str_res_mixer,
  str_res_filter,
  str_res_lfos,
  str_res_modulation,
  str_res_keyboard,
  str_res_off,
  str_res_on,
  str_res_tri,
  str_res_sqr,
  str_res_s_h,
  str_res_3,
  str_res__seq,
  str_res_lf1,
  str_res_lf2,
  str_res_seq,
  str_res_arp,
  str_res_whl,
  str_res_bnd,
  str_res_ofs,
  str_res_cv1,
  str_res_cv2,
  str_res_cv3,
  str_res_rnd,
  str_res_en1,
  str_res_en2,
  str_res_vel,
  str_res_not,
  str_res_gat,
  str_res_lfo1,
  str_res_lfo2,
  str_res_stpseq,
  str_res__arp,
  str_res_mwheel,
  str_res_bender,
  str_res_offset,
  str_res__cv1,
  str_res__cv2,
  str_res__cv3,
  str_res_random,
  str_res_env1,
  str_res_env2,
  str_res_velo,
  str_res_note,
  str_res_gate,
  str_res_270,
  str_res_300,
  str_res_360,
  str_res_480,
  str_res_720,
  str_res_960,
  str_res_start,
  str_res_length,
  str_res_touch_a_knob_to,
  str_res_assign_parameter,
  str_res_ready,
  str_res_for_os_update,
  str_res_patch_bank,
  str_res_step_sequencer,
  str_res_load,
  str_res_,
  str_res_save,
  str_res_extern,
  str_res_x2_ext,
  str_res__2_ext,
  str_res__4_ext,
  str_res__8_ext,
  str_res_mutable____v0_59,
  str_res_instruments_671,
  str_res_equal,
  str_res_just,
  str_res_pythag,
  str_res_1_4_eb,
  str_res_1_4_e,
  str_res_1_4_ea,
  str_res_bhaira,
  str_res_gunakr,
  str_res_marwa,
  str_res_shree,
  str_res_purvi,
  str_res_bilawa,
  str_res_yaman,
  str_res_kafi,
  str_res_bhimpa,
  str_res_darbar,
  str_res_bagesh,
  str_res_ragesh,
  str_res_khamaj,
  str_res_mimal,
  str_res_parame,
  str_res_ranges,
  str_res_ganges,
  str_res_kamesh,
  str_res_palas_,
  str_res_natbha,
  str_res_m_kaun,
  str_res_bairag,
  str_res_b_todi,
  str_res_chandr,
  str_res_kaushi,
  str_res_jogesh,
  str_res_rasia,
};

const prog_uint16_t lut_res_lfo_increments[] PROGMEM = {
       4,      4,      4,      4,      5,      5,      5,      6, 
       6,      7,      7,      7,      8,      8,      9,     10, 
      10,     11,     11,     12,     13,     14,     15,     15, 
      16,     17,     18,     20,     21,     22,     23,     25, 
      26,     28,     30,     32,     33,     35,     38,     40, 
      42,     45,     48,     50,     54,     57,     60,     64, 
      68,     72,     76,     81,     86,     91,     96,    102, 
     108,    115,    121,    129,    136,    145,    153,    162, 
     172,    183,    193,    205,    217,    230,    244,    259, 
     274,    291,    308,    327,    346,    367,    389,    412, 
     437,    463,    491,    520,    551,    584,    619,    657, 
     696,    738,    782,    828,    878,    931,    986,   1045, 
    1108,   1174,   1244,   1319,   1398,   1481,   1570,   1664, 
    1764,   1869,   1981,   2099,   2225,   2358,   2499,   2649, 
    2807,   2975,   3153,   3342,   3542,   3753,   3978,   4216, 
    4468,   4735,   5019,   5319,   5637,   5974,   6332,   6710, 
};
const prog_uint16_t lut_res_env_portamento_increments[] PROGMEM = {
   32766,  26512,  21682,  17903,  14912,  12521,  10590,   9018, 
    7727,   6659,   5769,   5023,   4394,   3860,   3405,   3015, 
    2679,   2389,   2137,   1917,   1725,   1556,   1408,   1277, 
    1160,   1057,    965,    882,    809,    743,    683,    629, 
     581,    537,    497,    461,    428,    398,    370,    345, 
     322,    301,    281,    263,    247,    232,    218,    205, 
     192,    181,    171,    161,    152,    144,    136,    129, 
     122,    116,    110,    104,     99,     94,     89,     85, 
      81,     77,     73,     70,     67,     64,     61,     58, 
      56,     53,     51,     49,     47,     45,     43,     41, 
      39,     38,     36,     35,     34,     32,     31,     30, 
      29,     28,     27,     26,     25,     24,     23,     22, 
      21,     21,     20,     19,     19,     18,     17,     17, 
      16,     16,     15,     15,     14,     14,     13,     13, 
      12,     12,     12,     11,     11,     11,     10,     10, 
      10,      9,      9,      9,      9,      8,      8,      8, 
};
const prog_uint16_t lut_res_oscillator_increments[] PROGMEM = {
    4389,   4393,   4397,   4401,   4405,   4409,   4413,   4417, 
    4421,   4425,   4429,   4433,   4437,   4441,   4445,   4449, 
    4453,   4457,   4461,   4465,   4469,   4473,   4477,   4481, 
    4485,   4489,   4493,   4497,   4501,   4505,   4509,   4513, 
    4517,   4522,   4526,   4530,   4534,   4538,   4542,   4546, 
    4550,   4554,   4558,   4563,   4567,   4571,   4575,   4579, 
    4583,   4587,   4591,   4596,   4600,   4604,   4608,   4612, 
    4616,   4621,   4625,   4629,   4633,   4637,   4641,   4646, 
    4650,   4654,   4658,   4662,   4667,   4671,   4675,   4679, 
    4684,   4688,   4692,   4696,   4700,   4705,   4709,   4713, 
    4717,   4722,   4726,   4730,   4735,   4739,   4743,   4747, 
    4752,   4756,   4760,   4765,   4769,   4773,   4777,   4782, 
    4786,   4790,   4795,   4799,   4803,   4808,   4812,   4816, 
    4821,   4825,   4830,   4834,   4838,   4843,   4847,   4851, 
    4856,   4860,   4865,   4869,   4873,   4878,   4882,   4887, 
    4891,   4895,   4900,   4904,   4909,   4913,   4917,   4922, 
    4926,   4931,   4935,   4940,   4944,   4949,   4953,   4958, 
    4962,   4967,   4971,   4976,   4980,   4985,   4989,   4994, 
    4998,   5003,   5007,   5012,   5016,   5021,   5025,   5030, 
    5034,   5039,   5043,   5048,   5052,   5057,   5062,   5066, 
    5071,   5075,   5080,   5084,   5089,   5094,   5098,   5103, 
    5107,   5112,   5117,   5121,   5126,   5131,   5135,   5140, 
    5145,   5149,   5154,   5158,   5163,   5168,   5172,   5177, 
    5182,   5186,   5191,   5196,   5201,   5205,   5210,   5215, 
    5219,   5224,   5229,   5233,   5238,   5243,   5248,   5252, 
    5257,   5262,   5267,   5271,   5276,   5281,   5286,   5290, 
    5295,   5300,   5305,   5310,   5314,   5319,   5324,   5329, 
    5334,   5338,   5343,   5348,   5353,   5358,   5363,   5367, 
    5372,   5377,   5382,   5387,   5392,   5397,   5401,   5406, 
    5411,   5416,   5421,   5426,   5431,   5436,   5441,   5446, 
    5450,   5455,   5460,   5465,   5470,   5475,   5480,   5485, 
    5490,   5495,   5500,   5505,   5510,   5515,   5520,   5525, 
    5530,   5535,   5540,   5545,   5550,   5555,   5560,   5565, 
    5570,   5575,   5580,   5585,   5590,   5595,   5600,   5605, 
    5610,   5615,   5620,   5625,   5630,   5636,   5641,   5646, 
    5651,   5656,   5661,   5666,   5671,   5676,   5682,   5687, 
    5692,   5697,   5702,   5707,   5712,   5718,   5723,   5728, 
    5733,   5738,   5743,   5749,   5754,   5759,   5764,   5769, 
    5775,   5780,   5785,   5790,   5795,   5801,   5806,   5811, 
    5816,   5822,   5827,   5832,   5837,   5843,   5848,   5853, 
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
};
const prog_uint16_t lut_res_fm_frequency_ratios[] PROGMEM = {
      32,     64,    128,    129,    181,    201,    256,    257, 
     362,    402,    448,    512,    514,    576,    704,    724, 
     768,    804,    886,   1024,   1086,   1206,   1280,   1448, 
    2048, 
};
const prog_uint16_t lut_res_scale_just[] PROGMEM = {
       0,     15,      5,     20,    -17,     -2,    -12,      2, 
      17,    -20,     -5,    -15, 
};
const prog_uint16_t lut_res_scale_pythagorean[] PROGMEM = {
       0,     15,      5,     -7,     10,     -2,    -12,      2, 
      17,    -20,     -5,     12, 
};
const prog_uint16_t lut_res_scale_1_4_eb[] PROGMEM = {
       0,      0,      0,      0,    -64,      0,      0,      0, 
       0,      0,      0,    -64, 
};
const prog_uint16_t lut_res_scale_1_4_e[] PROGMEM = {
       0,      0,      0,      0,    -64,      0,      0,      0, 
       0,      0,      0,      0, 
};
const prog_uint16_t lut_res_scale_1_4_ea[] PROGMEM = {
       0,      0,      0,      0,    -64,      0,      0,      0, 
       0,    -64,      0,      0, 
};
const prog_uint16_t lut_res_scale_bhairav[] PROGMEM = {
       0,    -12,  32767,  32767,    -17,     -2,  32767,      2, 
     -10,  32767,  32767,    -15, 
};
const prog_uint16_t lut_res_scale_gunakri[] PROGMEM = {
       0,     15,  32767,  32767,  32767,     -2,  32767,      2, 
      17,  32767,  32767,  32767, 
};
const prog_uint16_t lut_res_scale_marwa[] PROGMEM = {
       0,     15,  32767,  32767,    -17,  32767,    -12,  32767, 
   32767,    -20,  32767,    -15, 
};
const prog_uint16_t lut_res_scale_shree[] PROGMEM = {
       0,    -12,  32767,  32767,    -17,  32767,    -12,      2, 
     -10,  32767,  32767,    -15, 
};
const prog_uint16_t lut_res_scale_purvi[] PROGMEM = {
       0,     15,  32767,  32767,    -17,  32767,    -12,      2, 
      17,  32767,  32767,    -15, 
};
const prog_uint16_t lut_res_scale_bilawal[] PROGMEM = {
       0,  32767,      5,  32767,    -17,     -2,  32767,      2, 
   32767,      7,  32767,    -15, 
};
const prog_uint16_t lut_res_scale_yaman[] PROGMEM = {
       0,  32767,      5,  32767,     10,  32767,     15,      2, 
   32767,      7,  32767,     12, 
};
const prog_uint16_t lut_res_scale_kafi[] PROGMEM = {
       0,  32767,    -22,     -7,  32767,     -2,  32767,      2, 
   32767,    -20,     -5,  32767, 
};
const prog_uint16_t lut_res_scale_bhimpalasree[] PROGMEM = {
       0,  32767,      5,     20,  32767,     -2,  32767,      2, 
   32767,      7,     22,  32767, 
};
const prog_uint16_t lut_res_scale_darbari[] PROGMEM = {
       0,  32767,      5,     -7,  32767,     -2,  32767,      2, 
     -10,  32767,     -5,  32767, 
};
const prog_uint16_t lut_res_scale_rageshree[] PROGMEM = {
       0,  32767,      5,  32767,    -17,     -2,  32767,      2, 
   32767,    -20,     -5,  32767, 
};
const prog_uint16_t lut_res_scale_khamaj[] PROGMEM = {
       0,  32767,      5,  32767,    -17,     -2,  32767,      2, 
   32767,      7,     -5,     12, 
};
const prog_uint16_t lut_res_scale_mimal[] PROGMEM = {
       0,  32767,      5,     -7,  32767,     -2,  32767,      2, 
   32767,    -20,     -5,    -15, 
};
const prog_uint16_t lut_res_scale_parameshwari[] PROGMEM = {
       0,    -12,  32767,     -7,  32767,     -2,  32767,  32767, 
   32767,    -20,     -5,  32767, 
};
const prog_uint16_t lut_res_scale_rangeshwari[] PROGMEM = {
       0,  32767,      5,     -7,  32767,     -2,  32767,      2, 
   32767,  32767,  32767,    -15, 
};
const prog_uint16_t lut_res_scale_gangeshwari[] PROGMEM = {
       0,  32767,  32767,  32767,    -17,     -2,  32767,      2, 
     -10,  32767,     -5,  32767, 
};
const prog_uint16_t lut_res_scale_kameshwari[] PROGMEM = {
       0,  32767,      5,  32767,  32767,  32767,    -12,      2, 
   32767,    -20,     -5,  32767, 
};
const prog_uint16_t lut_res_scale_palas_kafi[] PROGMEM = {
       0,  32767,      5,     -7,  32767,     -2,  32767,      2, 
   32767,      7,     -5,  32767, 
};
const prog_uint16_t lut_res_scale_natbhairav[] PROGMEM = {
       0,  32767,      5,  32767,    -17,     -2,  32767,      2, 
     -10,  32767,  32767,    -15, 
};
const prog_uint16_t lut_res_scale_m_kauns[] PROGMEM = {
       0,  32767,      5,  32767,     10,     -2,  32767,  32767, 
     -10,  32767,     -5,  32767, 
};
const prog_uint16_t lut_res_scale_bairagi[] PROGMEM = {
       0,    -12,  32767,  32767,  32767,     -2,  32767,      2, 
   32767,  32767,     -5,  32767, 
};
const prog_uint16_t lut_res_scale_b_todi[] PROGMEM = {
       0,    -12,  32767,     -7,  32767,  32767,  32767,      2, 
   32767,  32767,     -5,  32767, 
};
const prog_uint16_t lut_res_scale_chandradeep[] PROGMEM = {
       0,  32767,  32767,     -7,  32767,     -2,  32767,      2, 
   32767,  32767,     -5,  32767, 
};
const prog_uint16_t lut_res_scale_kaushik_todi[] PROGMEM = {
       0,  32767,  32767,     -7,  32767,     -2,    -12,  32767, 
     -10,  32767,  32767,  32767, 
};
const prog_uint16_t lut_res_scale_jogeshwari[] PROGMEM = {
       0,  32767,  32767,     -7,    -17,     -2,  32767,  32767, 
   32767,    -20,     -5,  32767, 
};
const prog_uint16_t lut_res_arpeggiator_patterns[] PROGMEM = {
   21845,  30583,  62965,  46517,  28527,   2313,  18761,  21065, 
   18725,  56283,  30431,  43281,  54553,  28609,  53505, 
};
const prog_uint16_t lut_res_turbo_tempi[] PROGMEM = {
     270,    300,    360,    480,    720,    960, 
};
const prog_uint16_t lut_res_groove_swing[] PROGMEM = {
     127,    127,   -127,   -127,    127,    127,   -127,   -127, 
     127,    127,   -127,   -127,    127,    127,   -127,   -127, 
};
const prog_uint16_t lut_res_groove_shuffle[] PROGMEM = {
     127,   -127,    127,   -127,    127,   -127,    127,   -127, 
     127,   -127,    127,   -127,    127,   -127,    127,   -127, 
};
const prog_uint16_t lut_res_groove_push[] PROGMEM = {
     -63,    -63,    127,      0,   -127,      0,      0,     88, 
       0,      0,     88,    -50,    -88,      0,     88,      0, 
};
const prog_uint16_t lut_res_groove_lag[] PROGMEM = {
      19,     44,     93,     -4,     32,    -53,    -90,   -127, 
     117,     32,   -102,    -53,    105,    -53,     93,    -53, 
};
const prog_uint16_t lut_res_groove_human[] PROGMEM = {
      88,   -101,    107,    -95,     88,    -88,     50,    -38, 
      65,    -88,    101,    -95,    101,   -127,     63,    -31, 
};


PROGMEM const prog_uint16_t* lookup_table_table[] = {
  lut_res_lfo_increments,
  lut_res_env_portamento_increments,
  lut_res_oscillator_increments,
  lut_res_fm_frequency_ratios,
  lut_res_scale_just,
  lut_res_scale_pythagorean,
  lut_res_scale_1_4_eb,
  lut_res_scale_1_4_e,
  lut_res_scale_1_4_ea,
  lut_res_scale_bhairav,
  lut_res_scale_gunakri,
  lut_res_scale_marwa,
  lut_res_scale_shree,
  lut_res_scale_purvi,
  lut_res_scale_bilawal,
  lut_res_scale_yaman,
  lut_res_scale_kafi,
  lut_res_scale_bhimpalasree,
  lut_res_scale_darbari,
  lut_res_scale_kafi,
  lut_res_scale_rageshree,
  lut_res_scale_khamaj,
  lut_res_scale_mimal,
  lut_res_scale_parameshwari,
  lut_res_scale_rangeshwari,
  lut_res_scale_gangeshwari,
  lut_res_scale_kameshwari,
  lut_res_scale_palas_kafi,
  lut_res_scale_natbhairav,
  lut_res_scale_m_kauns,
  lut_res_scale_bairagi,
  lut_res_scale_b_todi,
  lut_res_scale_chandradeep,
  lut_res_scale_kaushik_todi,
  lut_res_scale_jogeshwari,
  lut_res_scale_yaman,
  lut_res_arpeggiator_patterns,
  lut_res_turbo_tempi,
  lut_res_groove_swing,
  lut_res_groove_shuffle,
  lut_res_groove_push,
  lut_res_groove_lag,
  lut_res_groove_human,
};

const prog_uint8_t wav_res_formant_sine[] PROGMEM = {
       0,      0,      0,      0,      0,      0,      0,      0, 
       0,      0,      0,      0,      0,      0,      0,      0, 
       0,      2,      2,      3,      3,      4,      5,      6, 
       7,      8,     10,     12,     14,     17,     20,     24, 
       0,      3,      4,      5,      6,      7,      9,     10, 
      12,     15,     18,     21,     26,     31,     37,     45, 
       0,      4,      5,      6,      8,      9,     11,     13, 
      16,     19,     23,     28,     34,     40,     49,     58, 
       0,      5,      6,      7,      8,     10,     12,     15, 
      17,     21,     25,     30,     36,     44,     53,     63, 
       0,      4,      5,      6,      8,      9,     11,     13, 
      16,     19,     23,     28,     34,     40,     49,     58, 
       0,      3,      4,      5,      6,      7,      9,     10, 
      12,     15,     18,     21,     26,     31,     37,     45, 
       0,      2,      2,      3,      3,      4,      5,      6, 
       7,      8,     10,     12,     14,     17,     20,     24, 
       0,      0,      0,      0,      0,      0,      0,      0, 
       0,      0,      0,      0,      0,      0,      0,      0, 
       0,     -2,     -2,     -3,     -3,     -4,     -5,     -6, 
      -7,     -8,    -10,    -12,    -14,    -17,    -20,    -24, 
       0,     -3,     -4,     -5,     -6,     -7,     -9,    -10, 
     -12,    -15,    -18,    -21,    -26,    -31,    -37,    -45, 
       0,     -4,     -5,     -6,     -8,     -9,    -11,    -13, 
     -16,    -19,    -23,    -28,    -34,    -40,    -49,    -58, 
       0,     -5,     -6,     -7,     -8,    -10,    -12,    -15, 
     -17,    -21,    -25,    -30,    -36,    -44,    -53,    -63, 
       0,     -4,     -5,     -6,     -8,     -9,    -11,    -13, 
     -16,    -19,    -23,    -28,    -34,    -40,    -49,    -58, 
       0,     -3,     -4,     -5,     -6,     -7,     -9,    -10, 
     -12,    -15,    -18,    -21,    -26,    -31,    -37,    -45, 
       0,     -2,     -2,     -3,     -3,     -4,     -5,     -6, 
      -7,     -8,    -10,    -12,    -14,    -17,    -20,    -24, 
};
const prog_uint8_t wav_res_formant_square[] PROGMEM = {
       0,      1,      1,      2,      2,      3,      3,      4, 
       4,      5,      6,      8,      9,     11,     13,     16, 
       0,      1,      1,      2,      2,      3,      3,      4, 
       4,      5,      6,      8,      9,     11,     13,     16, 
       0,      1,      1,      2,      2,      3,      3,      4, 
       4,      5,      6,      8,      9,     11,     13,     16, 
       0,      1,      1,      2,      2,      3,      3,      4, 
       4,      5,      6,      8,      9,     11,     13,     16, 
       0,      1,      1,      2,      2,      3,      3,      4, 
       4,      5,      6,      8,      9,     11,     13,     16, 
       0,      1,      1,      2,      2,      3,      3,      4, 
       4,      5,      6,      8,      9,     11,     13,     16, 
       0,      1,      1,      2,      2,      3,      3,      4, 
       4,      5,      6,      8,      9,     11,     13,     16, 
       0,      1,      1,      2,      2,      3,      3,      4, 
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
     102,    101,    100,    100,     99,     98,    100,    101, 
     103,    106,    109,    113,    117,    119,    124,    128, 
     131,    135,    138,    141,    145,    149,    152,    154, 
     156,    157,    158,    157,    156,    155,    155,    155, 
     155,    156,    159,    163,    169,    176,    183,    192, 
     203,    212,    221,    230,    238,    244,    249,    254, 
     255,    255,    255,    249,    238,    225,    213,    197, 
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
};
const prog_uint8_t wav_res_vowel_data[] PROGMEM = {
      27,     40,     89,    253,     16,     18,     51,     62, 
     220,     96,     15,     69,     93,    236,    112,     10, 
      84,    110,    218,    128,     23,     44,     87,    252, 
      16,     13,     29,     80,    216,      0,      6,     46, 
      81,    195,      0,      9,     51,     95,    243,      3, 
       6,     73,     99,    122,    233, 
};


const prog_uint8_t* waveform_table[] = {
  wav_res_formant_sine,
  wav_res_formant_square,
  wav_res_bandlimited_square_0,
  wav_res_bandlimited_square_1,
  wav_res_bandlimited_square_2,
  wav_res_bandlimited_square_3,
  wav_res_bandlimited_square_4,
  wav_res_bandlimited_square_5,
  wav_res_bandlimited_square_6,
  wav_res_bandlimited_saw_0,
  wav_res_bandlimited_saw_1,
  wav_res_bandlimited_saw_2,
  wav_res_bandlimited_saw_3,
  wav_res_bandlimited_saw_4,
  wav_res_bandlimited_saw_5,
  wav_res_bandlimited_square_6,
  wav_res_bandlimited_triangle_0,
  wav_res_bandlimited_triangle_1,
  wav_res_bandlimited_triangle_2,
  wav_res_bandlimited_triangle_3,
  wav_res_bandlimited_triangle_4,
  wav_res_bandlimited_triangle_5,
  wav_res_bandlimited_square_6,
  wav_res_wavetable,
  wav_res_vowel_data,
};

const prog_uint8_t chr_res_special_characters[] PROGMEM = {
       0,      0,      0,      0,      0,      0,      0,      0, 
       2,      3,      3,      2,      2,     14,     30,     12, 
       0,      0,      0,      4,      4,     14,     17,     31, 
       4,     14,     21,      4,      4,      4,      4,      0, 
       0,      4,      4,      4,      4,     21,     14,      4, 
       0,      0,      0,      8,     21,      2,      0,      0, 
       8,     20,      9,     21,      3,      5,     17,     14, 
      14,     17,     31,     17,     23,     21,     21,      0, 
};


const prog_uint8_t* character_table[] = {
  chr_res_special_characters,
};


}  // namespace hardware_shruti
