garbage2garbage/shruti1/hardware/hal/timer.h

// Copyright 2009 Emilie Gillet.
//
// Author: Emilie Gillet (emilie.o.gillet@gmail.com)
//
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
// -----------------------------------------------------------------------------
//
// Definitions of timer and related PWM registers.

#ifndef HARDWARE_HAL_TIMER_H_
#define HARDWARE_HAL_TIMER_H_

// interrupt.h is not strictly needed here, but .cc files including the timer
// classes are likely to also define interrupt handlers (and we have macros for
// that).
#include <avr/interrupt.h>
#include <avr/io.h>

#include "hardware/hal/hal.h"

namespace hardware_hal {

SpecialFunctionRegister(TCCR0A);
SpecialFunctionRegister(TCCR0B);
SpecialFunctionRegister(TCCR1A);
SpecialFunctionRegister(TCCR1B);
SpecialFunctionRegister(TCCR2A);
SpecialFunctionRegister(TCCR2B);
SpecialFunctionRegister(TIMSK0);
SpecialFunctionRegister(TIMSK1);
SpecialFunctionRegister(TIMSK2);
SpecialFunctionRegister(TCNT0);
SpecialFunctionRegister(TCNT1);
SpecialFunctionRegister(TCNT2);
SpecialFunctionRegister(OCR0A);
SpecialFunctionRegister(OCR0B);
SpecialFunctionRegister(OCR1A);
SpecialFunctionRegister(OCR1B);
SpecialFunctionRegister(OCR2A);
SpecialFunctionRegister(OCR2B);

enum TimerMode {
  TIMER_NORMAL = 0,
  TIMER_PWM_PHASE_CORRECT = 1,
  TIMER_CTC = 2,
  TIMER_FAST_PWM = 3,
};

template<typename StatusRegisterA,
         typename StatusRegisterB,
         typename ModeRegister,
         typename ValueRegister,
         bool tweakable>
struct TimerImpl {
  typedef StatusRegisterA A;
  typedef StatusRegisterB B;
  
  static inline uint8_t value() {
    return *ValueRegister::ptr();
  }
  
  static inline void Start() {
    if (!tweakable) return;
    *ModeRegister::ptr() |= 1;
  }
  static inline void Stop() {
    if (!tweakable) return;
    *ModeRegister::ptr() &= ~1;
  }
  static inline void set_mode(TimerMode mode) {
    if (!tweakable) return;
    // Sets the mode registers.
    *StatusRegisterA::ptr() = (*StatusRegisterA::ptr() & 0xfc) | mode;
  }
  // Timer 0 (or Timer 1 in fast PWM mode):
  // value | 0 / 1 in fast mode | 1 / 0 in accurate mode
  // ---------------------------------------------------
  // 1     | 62.5 kHz           | 31.2 kHz
  // 2     | 7.81 kHz           | 3.91 kHz
  // 3     | 976 Hz             | 488 Hz
  // 4     | 244 Hz             | 122 Hz
  // 5     | 61 Hz              | 30 Hz
  //
  // Timer 2
  // value | accurate  | fast
  // ----------------------------
  // 1     | 31.2 kHz  | 62.5 kHz
  // 2     | 3.91 kHz  | 7.81 kHz
  // 3     | 976 Hz    | 1.95 kHz
  // 4     | 488 Hz    | 976 Hz
  // 5     | 244 Hz    | 488 Hz
  // 6     | 122 Hz    | 244 Hz
  // 7     | 30 Hz     | 60 Hz
  static inline void set_prescaler(uint8_t prescaler) {
    if (!tweakable) return;
    *StatusRegisterB::ptr() = (*StatusRegisterB::ptr() & 0xf8) | prescaler;
  }
};

template<int n>
struct NumberedTimer { };

// Timer<0> cannot be modified / stopped / started by default, because the real
// time clock (Delay(), milliseconds()) uses it.
template<> struct NumberedTimer<0> {
  typedef TimerImpl<
      TCCR0ARegister,
      TCCR0BRegister,
      TIMSK0Register,
      TCNT0Register,
      false> Impl;
};

template<> struct NumberedTimer<1> {
  typedef TimerImpl<
      TCCR1ARegister,
      TCCR1BRegister,
      TIMSK1Register,
      TCNT1Register,
      true> Impl;
};

template<> struct NumberedTimer<2> {
  typedef TimerImpl<
      TCCR2ARegister,
      TCCR2BRegister,
      TIMSK2Register,
      TCNT2Register,
      true> Impl;
};

template<int n>
struct Timer {
  typedef typename NumberedTimer<n>::Impl Impl;
  static inline uint8_t value() { return Impl::value(); }
  static inline void Start() { Impl::Start(); }
  static inline void Stop() { Impl::Stop(); }
  static inline void set_mode(TimerMode mode) { Impl::set_mode(mode); }
  static inline void set_prescaler(uint8_t prescaler) {
    Impl::set_prescaler(prescaler);
  }
};

template<typename Timer, uint8_t enabled_flag, typename PwmRegister>
struct PwmChannel {
  typedef BitInRegister<typename Timer::Impl::A, enabled_flag> EnabledBit;
  enum {
    analog = 1
  };
  static inline void Start() {
    EnabledBit::set();
  }
  static inline void Stop() {
    EnabledBit::clear();
  }
  static inline void Write(uint8_t value) {
    *PwmRegister::ptr() = value;
  }
};

struct NoPwmChannel {
  enum {
    analog = 0
  };
  static inline void Start() { }
  static inline void Stop() { }
  static inline void Write(uint8_t value) { }
};

typedef PwmChannel<Timer<0>, COM0A1, OCR0ARegister> PwmChannel0A;
typedef PwmChannel<Timer<0>, COM0B1, OCR0BRegister> PwmChannel0B;
typedef PwmChannel<Timer<1>, COM1A1, OCR1ARegister> PwmChannel1A;
typedef PwmChannel<Timer<1>, COM1B1, OCR1BRegister> PwmChannel1B;
typedef PwmChannel<Timer<2>, COM2A1, OCR2ARegister> PwmChannel2A;
typedef PwmChannel<Timer<2>, COM2B1, OCR2BRegister> PwmChannel2B;

// A definition of Timer<0> that can be adjusted / started / stopped, used for
// example in initialization code.
typedef TimerImpl<
    TCCR0ARegister,
    TCCR0BRegister,
    TIMSK0Register,
    TCNT0Register,
    true> MutableTimer0;

// Readable aliases for timer interrupts.
#define TIMER_0_TICK ISR(TIMER0_OVF_vect)
#define TIMER_1_TICK ISR(TIMER1_OVF_vect)
#define TIMER_2_TICK ISR(TIMER2_OVF_vect)

}  // namespace hardware_hal

#endif   // HARDWARE_HAL_TIMER_H_
