garbage2garbage/shruti1/hardware/shruti/synthesis_engine.h

// Copyright 2009 Emilie Gillet.
//
// Author: Emilie Gillet (emilie.o.gillet@gmail.com)
//
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
// -----------------------------------------------------------------------------
//
// Main synthesis engine. Everything is in static methods because this allows
// the compiler to compute in advance the address of all objects, and use direct
// addressing like:
// lds r18, 0x04e4
//
// instead of ugly indirect addressing like:
// subi r28, 0xf1
// sbci r29, 0xfD
// ld r18, Y
// ldd  r19, Y+1  ; 0x01
//
// This transformation from a class that would be used as a singleton anyway,
// to a "class" with only static methods/member variables yielded faster, leaner
// code in many places and has since been widely adopted in the code.
//
// Note that a polyphonic synth would need several voices object - in this case
// this transformation should not be applied to the Voice class. Since, for now
// only the monophonic mode is supported, Voice is also "static'ified".

#ifndef HARDWARE_SHRUTI_SYNTHESIS_ENGINE_H_
#define HARDWARE_SHRUTI_SYNTHESIS_ENGINE_H_

#include "hardware/shruti/shruti.h"

#include "hardware/midi/midi.h"
#include "hardware/shruti/envelope.h"
#include "hardware/shruti/lfo.h"
#include "hardware/shruti/patch.h"

#include "hardware/shruti/voice_controller.h"

namespace hardware_shruti {

// Used for MIDI -> oscillator increment conversion.
static const int16_t kLowestNote = 0 * 128;
static const int16_t kHighestNote = 108 * 128;
static const int16_t kOctave = 12 * 128;
static const int16_t kPitchTableStart = 96 * 128;

static const uint8_t kNumLfos = 2;
static const uint8_t kNumEnvelopes = 2;
static const uint8_t kNumOscillators = 2;

class Voice {
 public:
  Voice() { }
  static void Init();

  // Called whenever a new note is played, manually or through the arpeggiator.
  static void Trigger(uint8_t note, uint8_t velocity, uint8_t legato);

  // Move this voice to the release stage.
  static void Release() { TriggerEnvelope(RELEASE); }

  // Move this voice to the release stage.
  static void Kill() { TriggerEnvelope(DEAD); }

  static void Audio();
  static void Control();

  // Called whenever a write to the CV analog outputs has to be made.
  static inline uint8_t cutoff()  {
    return modulation_destinations_[MOD_DST_FILTER_CUTOFF];
  }
  static inline uint8_t vca()  {
    return modulation_destinations_[MOD_DST_VCA];
  }
  static inline uint8_t resonance()  {
    return modulation_destinations_[MOD_DST_FILTER_RESONANCE];
  }
  static inline uint8_t dead()  { return dead_; }
  static inline uint8_t signal()  { return signal_; }
  static inline uint8_t modulation_source(uint8_t i) {
    return modulation_sources_[i - kNumGlobalModulationSources];
  }
  static uint8_t modulation_destination(uint8_t i) {
    return modulation_destinations_[i];
  }
  static Envelope* mutable_envelope(uint8_t i) { return &envelope_[i]; }
  static void TriggerEnvelope(uint8_t stage);
  
 private:
  // Envelope generators.
  static Envelope envelope_[kNumEnvelopes];
  static uint8_t dead_;

  // Counters/phases for the pitch envelope generator (portamento).
  // Pitches are stored on 14 bits, the 7 highest bits are the MIDI note value,
  // the 7 lowest bits are used for fine-tuning.
  static int16_t pitch_increment_;
  static int16_t pitch_target_;
  static int16_t pitch_value_;

  // The voice-specific modulation sources are from MOD_SRC_ENV_1 to
  // MOD_SRC_GATE.
  static uint8_t modulation_sources_[kNumVoiceModulationSources];

  // Value of all the stuff controlled by the modulators, scaled to the value
  // they will be used for. MOD_DST_FILTER_RESONANCE is the last entry
  // in the modulation destinations enum.
  static int8_t modulation_destinations_[kNumModulationDestinations];
  
  static uint8_t signal_;
  
  static uint8_t osc1_phase_msb_;

  DISALLOW_COPY_AND_ASSIGN(Voice);
};

class SynthesisEngine : public hardware_midi::MidiDevice {
  friend class Voice;

 public:
  SynthesisEngine() { }
  static void Init();

  // Forwarded to the controller.
  static void NoteOn(uint8_t channel, uint8_t note, uint8_t velocity);
  static void NoteOff(uint8_t channel, uint8_t note, uint8_t velocity);
  
  // Handled.
  static void ControlChange(uint8_t channel, uint8_t controller, uint8_t value);
  static void PitchBend(uint8_t channel, uint16_t pitch_bend);
  static void AllSoundOff(uint8_t channel);
  static void ResetAllControllers(uint8_t channel);
  static void AllNotesOff(uint8_t channel);
  static void OmniModeOff(uint8_t channel);
  static void OmniModeOn(uint8_t channel);
  static void Reset();
  static void Clock();
  static void Start();
  static void Stop();
  static void SysExStart();
  static void SysExByte(uint8_t sysex_byte);
  static void SysExEnd();
  static uint8_t CheckChannel(uint8_t channel);
  
  static void Audio();
  static void Control();
  
  // Patch manipulation stuff.
  static void SetParameter(uint8_t parameter_index, uint8_t parameter_value);
  static inline uint8_t GetParameter(uint8_t parameter_index) {
    const uint8_t* base = &patch_.keep_me_at_the_top;
    return base[parameter_index + 1];
  }
  static uint8_t sequence_step(uint8_t step) {
    return patch_.sequence_step(step);
  }
  static void set_sequence_step(uint8_t step, uint8_t value) {
    patch_.set_sequence_step(step, value);
  }
  static void set_cv(uint8_t cv, uint8_t value) {
    modulation_sources_[MOD_SRC_CV_1 + cv] = value;
  }
  static uint8_t oscillator_decimation() { return oscillator_decimation_; }
  static void ResetPatch();
  // Variables dependent on parameters (increments) are recomputed in
  // SetParameter when the related parameter is modified. Sometimes, the patch
  // is modified all at once without any call to SetParameter (for example when
  // loading a patch from the EEPROM)... so in this case we need to recompute
  // all the related variables.
  static inline void TouchPatch() {
    UpdateModulationIncrements();
    UpdateOscillatorAlgorithms();
    controller_.UpdateArpeggiatorParameters(patch_);
  }
  static inline const Patch& patch() { return patch_; }
  static inline const VoiceController& voice_controller() {
    return controller_;
  }
  static inline VoiceController* mutable_voice_controller() {
    return &controller_;
  }
  static inline Patch* mutable_patch() { return &patch_; }
  
  // These variables are sent to I/O pins, and are made accessible here.
  static inline uint8_t modulation_source(uint8_t i, uint8_t j) {
    if (j < kNumGlobalModulationSources) {
      return modulation_sources_[j];
    } else {
      return voice_[i].modulation_source(j);
    }
  }
  static const Voice& voice(uint8_t i) { return voice_[i]; }
 private:
  // Value of global modulation parameters, scaled to 0-255;
  static uint8_t modulation_sources_[kNumGlobalModulationSources];
  
  static Patch patch_;
  static Lfo lfo_[kNumLfos];
  static uint8_t num_lfo_reset_steps_;  // resync the LFO every n-th step.
  static uint8_t lfo_reset_counter_;
  static uint8_t lfo_to_reset_;
  static Voice voice_[kNumVoices];
  static VoiceController controller_;
  static uint8_t oscillator_decimation_;
  static uint8_t nrpn_parameter_number_;
  static uint8_t data_entry_msb_;
  static uint8_t ignore_note_off_messages_;

  // Called whenever a parameter related to LFOs/envelopes is modified (for now
  // everytime a parameter is modified by the user).
  static void UpdateModulationIncrements();
  
  // Called whenever a parameter related to oscillators is called.
  static void UpdateOscillatorAlgorithms();
  
  DISALLOW_COPY_AND_ASSIGN(SynthesisEngine);
};

extern SynthesisEngine engine;

}  // namespace hardware_shruti

#endif  // HARDWARE_SHRUTI_SYNTHESIS_ENGINE_H_
