garbage2garbage/shruti1/hardware/hal/pretty_printer.h

// Copyright 2009 Olivier Gillet.
//
// Author: Olivier Gillet (ol.gillet@gmail.com)
//
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
// -----------------------------------------------------------------------------
//
// Pretty printer. Wraps any module implementing the basic Output interface
// (in fact, just a Write method), and provide string and integer formatting
// using the << stream operator.

#ifndef HARDWARE_HAL_PRETTY_PRINTER_H_
#define HARDWARE_HAL_PRETTY_PRINTER_H_

#include "hardware/utils/string.h"

using hardware_utils::Itoa;
using hardware_utils::TypeInfo;

namespace hardware_hal {

enum EndOfLine {
  endl = 0
};

template<typename Output>
struct PrettyPrinter {
  static void Print(const char* string) {
    while (*string) {
      Output::Write(*string++);
    }
  }
  static void Print(uint8_t byte) {
    Output::Write(byte);
  }
  static void Print(char byte) {
    Output::Write(byte);
  }
  static void Print(uint16_t value) {
    char buffer[TypeInfo<uint16_t>::max_size + 1];
    Itoa(value, TypeInfo<uint16_t>::max_size + 1, buffer);
    Print(buffer);
  }
  static void Print(int16_t value) {
    char buffer[TypeInfo<int16_t>::max_size + 1];
    Itoa(value, TypeInfo<int16_t>::max_size + 1, buffer);
    Print(buffer);
  }
  static void Print(uint32_t value) {
    char buffer[TypeInfo<uint32_t>::max_size + 1];
    Itoa(value, TypeInfo<uint32_t>::max_size + 1, buffer);
    Print(buffer);
  }
  static void Print(EndOfLine e) {
    Print('\r');
    Print('\n');
  }
  template<class T>
  inline PrettyPrinter<Output>& operator<<(const T value) {
    Print(value);
    return *this;
  }
};

}  // namespace hardware_hal

#endif   // HARDWARE_HAL_PRETTY_PRINTER_H_
